eigenco/RPiISA/20231105-8088/cputable.h

unsigned char instructions[] = {
0x03, 0x03, 0x05, 0x05, 0x06, 0x07, 0x05, 0x03,
0x01, 0x01, 0x01, 0x01, 0x01, 0x01, 0x01, 0x01,
0x0B, 0x0B, 0x0A, 0x0A, 0x0B, 0x0B, 0x0A, 0x0B,
0x09, 0x09, 0x09, 0x09, 0x07, 0x07, 0x19, 0x1A,
0x09, 0x09, 0x09, 0x09, 0x07, 0x07, 0x19, 0x30,
0x09, 0x09, 0x09, 0x09, 0x07, 0x07, 0x19, 0x1A,
0x09, 0x09, 0x09, 0x09, 0x07, 0x07, 0x19, 0x1A,
0x09, 0x09, 0x09, 0x09, 0x07, 0x07, 0x1B, 0x1C,
0x09, 0x09, 0x09, 0x09, 0x07, 0x07, 0x1B, 0x1C,
0x09, 0x09, 0x09, 0x09, 0x07, 0x07, 0x1B, 0x1D,
0x09, 0x09, 0x09, 0x09, 0x07, 0x07, 0x1B, 0x1D,
0x02, 0x02, 0x02, 0x02, 0x02, 0x02, 0x02, 0x02,
0x02, 0x02, 0x02, 0x02, 0x02, 0x02, 0x02, 0x02,
0x03, 0x03, 0x03, 0x03, 0x03, 0x03, 0x03, 0x03,
0x04, 0x04, 0x04, 0x04, 0x04, 0x04, 0x04, 0x04,
0x33, 0x36, 0x34, 0x34, 0x34, 0x34, 0x34, 0x34,
0x37, 0x37, 0x37, 0x37, 0x34, 0x34, 0x34, 0x34,
0x00, 0x00, 0x00, 0x00, 0x00, 0x00, 0x00, 0x00,
0x00, 0x00, 0x00, 0x00, 0x00, 0x00, 0x00, 0x00,
0x08, 0x08, 0x08, 0x08, 0x0F, 0x0F, 0x18, 0x18,
0x09, 0x09, 0x09, 0x09, 0x0A, 0x0A, 0x0A, 0x0A,
0x10, 0x10, 0x10, 0x10, 0x10, 0x10, 0x10, 0x10,
0x1E, 0x1F, 0x20, 0x35, 0x21, 0x22, 0x23, 0x24,
0x0B, 0x0B, 0x0B, 0x0B, 0x11, 0x11, 0x12, 0x12,
0x2F, 0x2F, 0x11, 0x11, 0x11, 0x11, 0x12, 0x12,
0x01, 0x01, 0x01, 0x01, 0x01, 0x01, 0x01, 0x01,
0x01, 0x01, 0x01, 0x01, 0x01, 0x01, 0x01, 0x01,
0x0C, 0x0C, 0x13, 0x13, 0x25, 0x25, 0x14, 0x14,
0x31, 0x32, 0x13, 0x13, 0x26, 0x27, 0x28, 0x13,
0x0C, 0x0C, 0x0C, 0x0C, 0x29, 0x2A, 0x2B, 0x2C,
0x35, 0x35, 0x35, 0x35, 0x35, 0x35, 0x35, 0x35,
0x0D, 0x0D, 0x0D, 0x0D, 0x15, 0x15, 0x16, 0x16,
0x06, 0x07, 0x06, 0x07, 0x0C, 0x0C, 0x0C, 0x0C,
0x00, 0x00, 0x00, 0x00, 0x00, 0x00, 0x01, 0x00,
0x0B, 0x0B, 0x0A, 0x0A, 0x0B, 0x0B, 0x0B, 0x0B,
0x03, 0x03, 0x05, 0x05, 0x06, 0x07, 0x05, 0x03,
0x01, 0x01, 0x01, 0x01, 0x01, 0x01, 0x01, 0x01,
0x0B, 0x0B, 0x0A, 0x0A, 0x0B, 0x0B, 0x0A, 0x0B,
0x09, 0x09, 0x09, 0x09, 0x07, 0x07, 0x19, 0x1A,
0x09, 0x09, 0x09, 0x09, 0x07, 0x07, 0x19, 0x30,
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
